BlessedRebuS/Proximity-Light/Light-Sensor/img/Usbasp 10 pin atmega328p.png

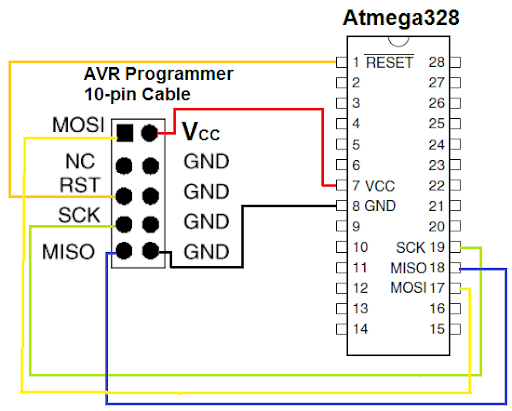
Light-Sensor/img/Usbasp 10 pin atmega328p.png
